blastrock/ExtraDox/Pictures/2.jpg

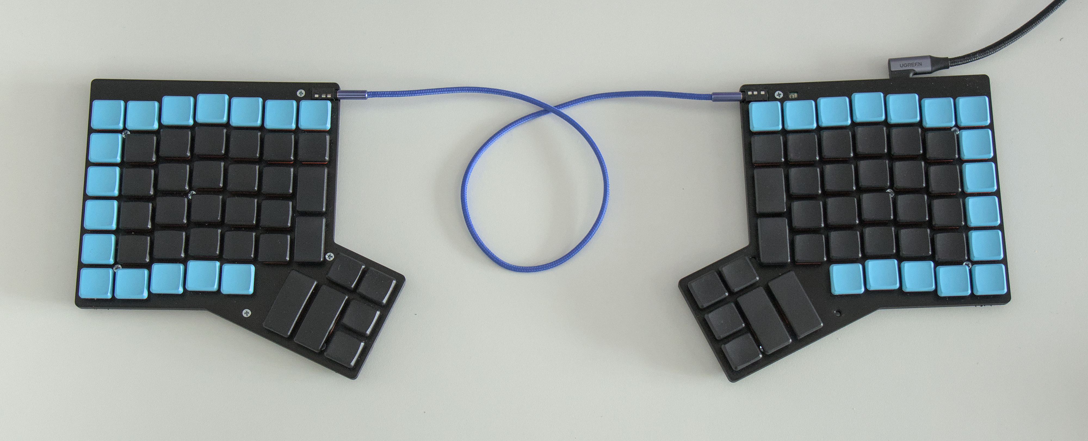
Pictures/2.jpg
