blastrock/ExtraDox/Case/positions.scad

rightSwitchPositions = [
  [47.650, -51.610, 0.000],
  [-9.500, -46.838, 0.000],
  [-28.550, -48.435, 0.000],
  [47.650, -32.560, 0.000],
  [-9.500, -27.788, 0.000],
  [-28.550, -29.385, 0.000],
  [-66.650, -25.893, 90.000],
  [47.650, -13.510, 0.000],
  [9.550, -10.335, 0.000],
  [-9.500, -8.738, 0.000],
  [-28.550, -10.335, 0.000],
  [-47.600, -11.605, 0.000],
  [47.650, 5.540, 0.000],
  [28.600, 5.540, 0.000],
  [9.550, 8.715, 0.000],
  [-9.500, 10.312, 0.000],
  [-28.550, 8.715, 0.000],
  [-47.600, 7.445, 0.000],
  [-66.650, 2.682, 90.000],
  [-57.737, -61.473, 115.000],
  [-88.240, -86.208, 25.000],
  [-75.001, -69.525, 115.000],
  [-96.291, -68.941, 25.000],
  [-104.341, -51.676, 25.000],
  [9.550, -48.435, 0.000],
  [-87.076, -43.627, 25.000],
  [47.650, 24.590, 0.000],
  [-28.550, 27.765, 0.000],
  [-9.500, 29.362, 0.000],
  [9.550, 27.765, 0.000],
  [28.600, 24.587, 0.000],
  [-47.600, 26.492, 0.000],
  [-66.650, 26.492, 0.000],
  [9.550, -29.385, 0.000],
  [-47.600, -30.655, 0.000],
  [28.600, -13.510, 0.000],
  [28.600, -32.560, 0.000],
  [28.600, -51.610, 0.000],
  [-66.650, 45.542, 0.000],
  [-47.600, 45.542, 0.000],
  [-28.550, 46.815, 0.000],
  [28.600, 43.637, 0.000],
  [-9.500, 48.412, 0.000],
  [9.550, 46.815, 0.000],
  [47.650, 43.640, 0.000],
];

rightHolePositions = [
  [-77.470, -34.290],
  [38.125, -42.212],
  [-57.483, 59.690],
  [-75.159, -83.868],
  [0.000, -0.000],
  [38.402, 34.290],
  [-33.604, -66.167],
];

rightUsbPosition = 
[12.380, 59.199]
;

rightResetPosition = 
[-15.240, 59.690]
;

rightJackPosition = 
[-76.225, 59.055]
;

rightLedPositions = [
[-50.796, 59.055],
[-49.211, 59.055],
[-47.625, 59.055],
];

leftSwitchPositions = [
  [66.650, 45.542, 0.000],
  [66.650, 26.492, 0.000],
  [-47.650, 24.590, 0.000],
  [9.500, -8.738, 0.000],
  [-28.600, -51.610, 0.000],
  [66.650, -25.893, -90.000],
  [96.291, -68.941, -25.000],
  [57.737, -61.473, -115.000],
  [-47.650, 43.640, 0.000],
  [28.550, -29.385, 0.000],
  [-47.650, -13.510, 0.000],
  [9.500, 48.412, 0.000],
  [47.600, -11.605, 0.000],
  [28.550, 27.765, 0.000],
  [47.600, -30.655, 0.000],
  [-9.550, -48.435, 0.000],
  [-47.650, -51.610, 0.000],
  [104.341, -51.676, -25.000],
  [28.550, 8.715, 0.000],
  [-28.600, -13.510, 0.000],
  [47.600, 7.445, 0.000],
  [9.500, -46.838, 0.000],
  [-28.600, 24.587, 0.000],
  [-9.550, 8.715, 0.000],
  [9.500, 29.362, 0.000],
  [-9.550, 27.765, 0.000],
  [47.600, 45.542, 0.000],
  [66.650, 2.682, -90.000],
  [9.500, 10.312, 0.000],
  [28.550, -10.335, 0.000],
  [28.550, -48.435, 0.000],
  [-28.600, 43.637, 0.000],
  [-28.600, 5.540, 0.000],
  [-9.550, 46.815, 0.000],
  [47.600, 26.492, 0.000],
  [-47.650, 5.540, 0.000],
  [-9.550, -29.385, 0.000],
  [-47.650, -32.560, 0.000],
  [9.500, -27.788, 0.000],
  [-9.550, -10.335, 0.000],
  [28.550, 46.815, 0.000],
  [75.001, -69.525, -115.000],
  [87.076, -43.627, -25.000],
  [88.240, -86.208, -25.000],
  [-28.600, -32.560, 0.000],
];

leftHolePositions = [
  [75.159, -83.868],
  [77.470, -34.290],
  [-38.402, 34.290],
  [33.604, -66.167],
  [57.483, 59.690],
  [-38.125, -42.212],
  [0.000, -0.000],
];

leftJackPosition = 
[76.225, 59.055]
;
